monsonite/TICK_TALK/TICK_04_08_24.jpg

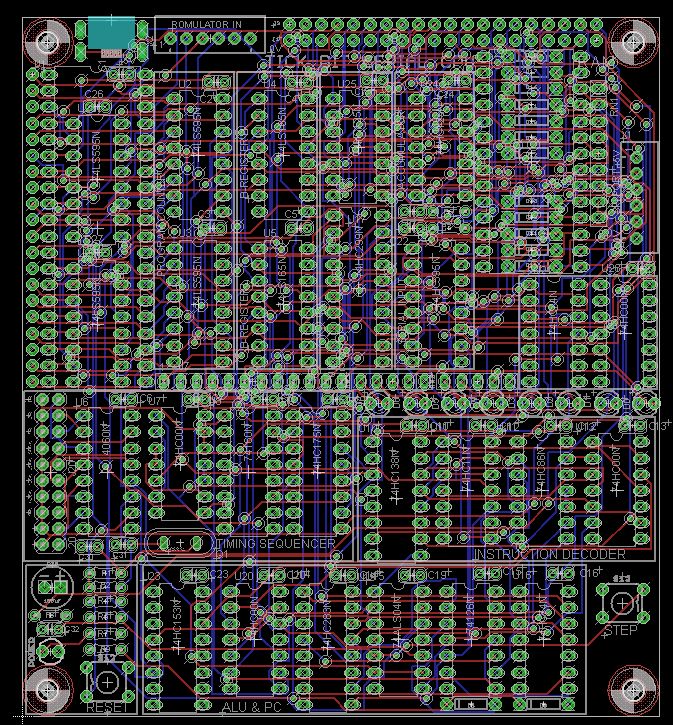
TICK_04_08_24.jpg
