monsonite/TICK_TALK/ALU_PC_schematic.jpg

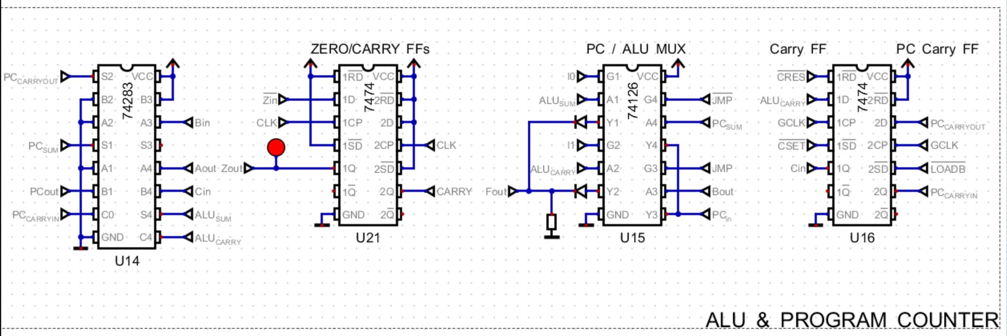
ALU_PC_schematic.jpg
