monsonite/TICK_TALK/Prototype_Program_Counter.jpg

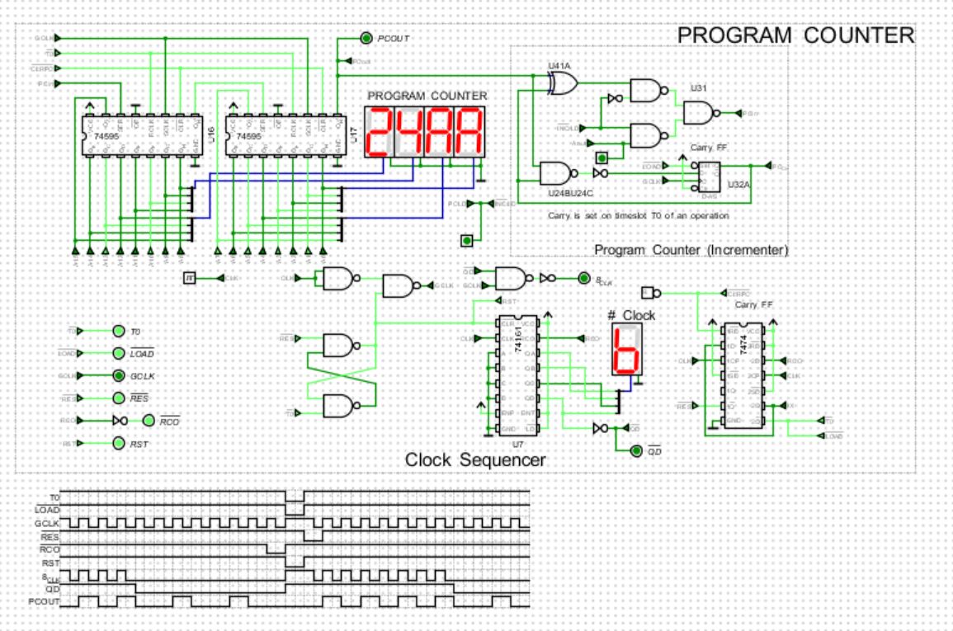
Prototype_Program_Counter.jpg
