monsonite/TICK_TALK/TPG_schematic.jpg

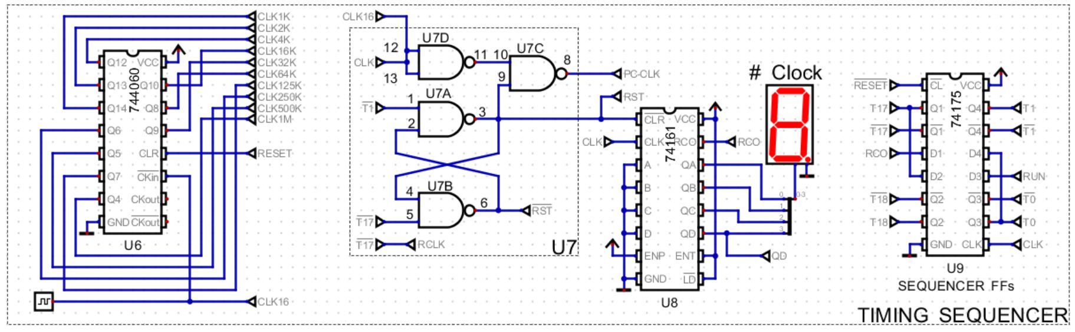
TPG_schematic.jpg
