monsonite/TICK_TALK/Build_step_1A_TPG.jpg

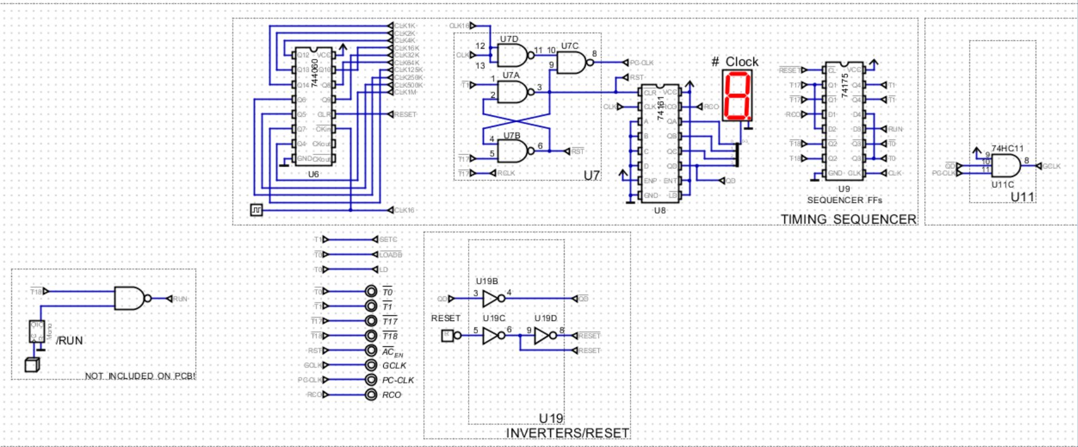
Build_step_1A_TPG.jpg
