monsonite/TICK_TALK/Build_Step_3A_ROMulator.jpg

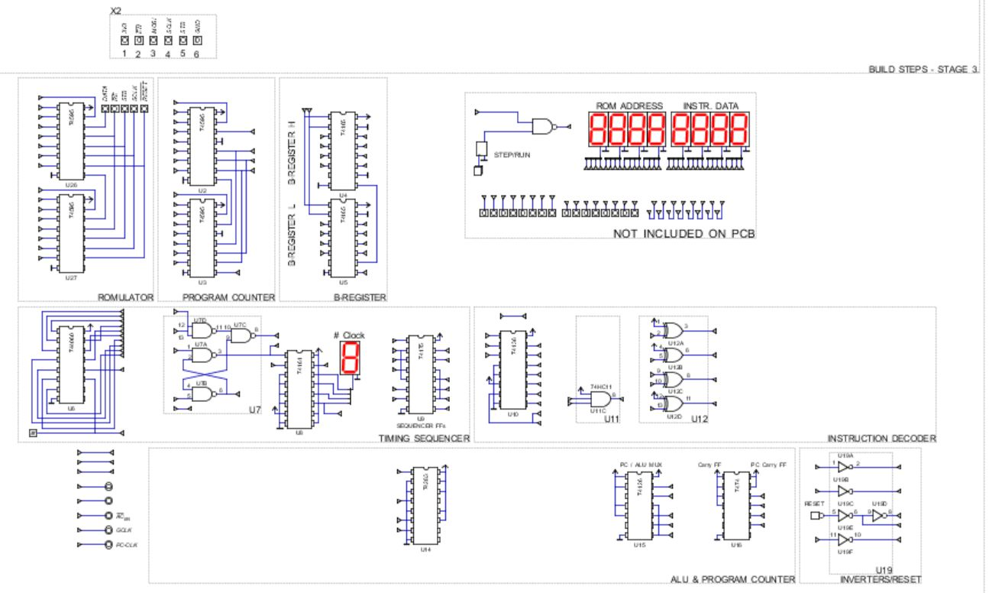
Build_Step_3A_ROMulator.jpg
