monsonite/TICK_TALK/Build_step_4A_ALU_Instruction_Decoder.jpg

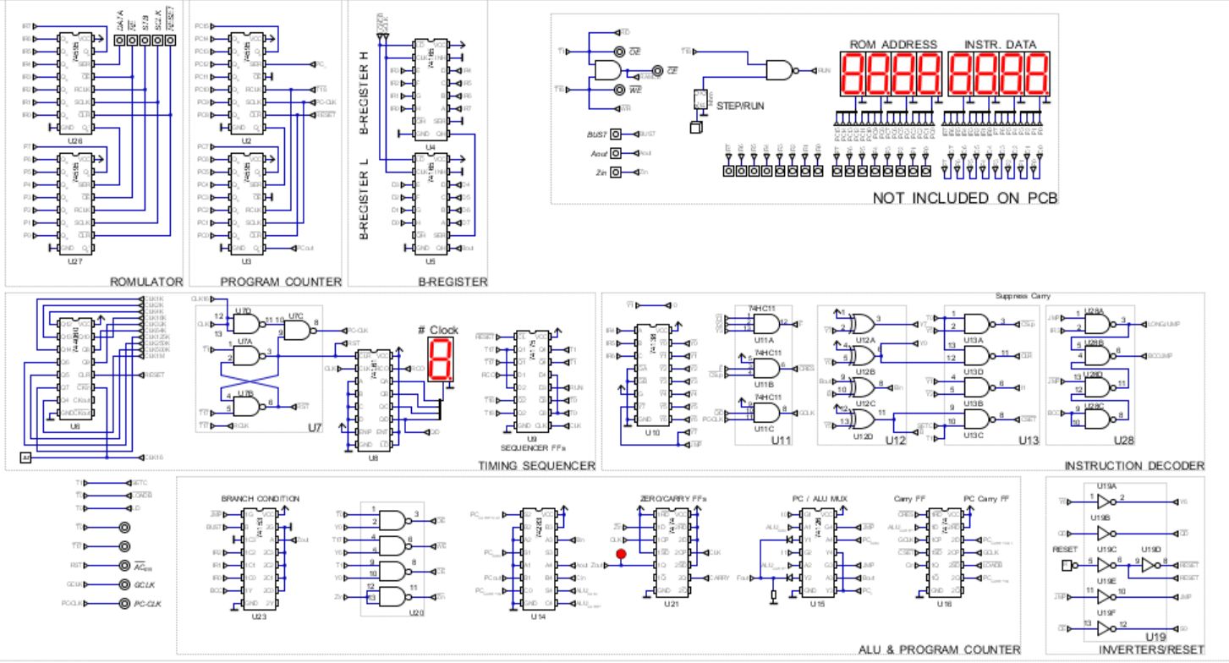
Build_step_4A_ALU_Instruction_Decoder.jpg
