monsonite/TICK_TALK/Build_Step_5A_RAM_Buffers_Accumulator_Serial_Input.jpg

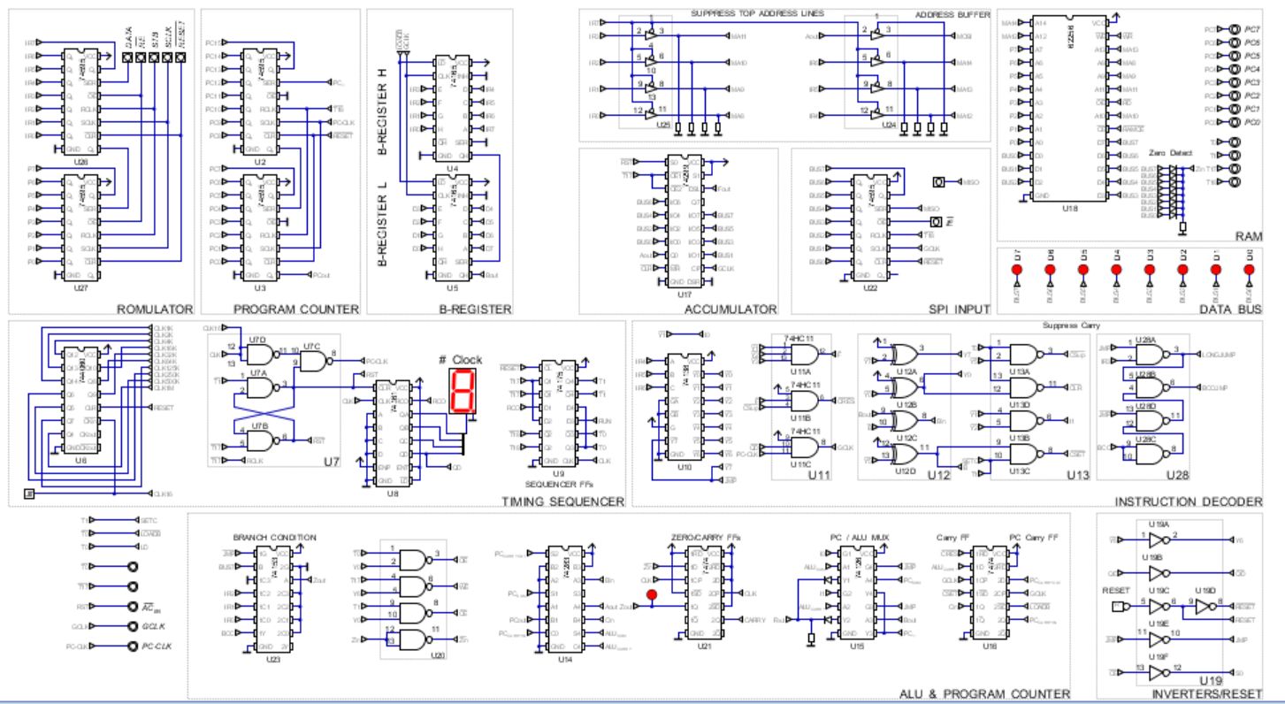
Build_Step_5A_RAM_Buffers_Accumulator_Serial_Input.jpg
