monsonite/TICK_TALK/Bulid_step_2A_B-reg_PC.jpg

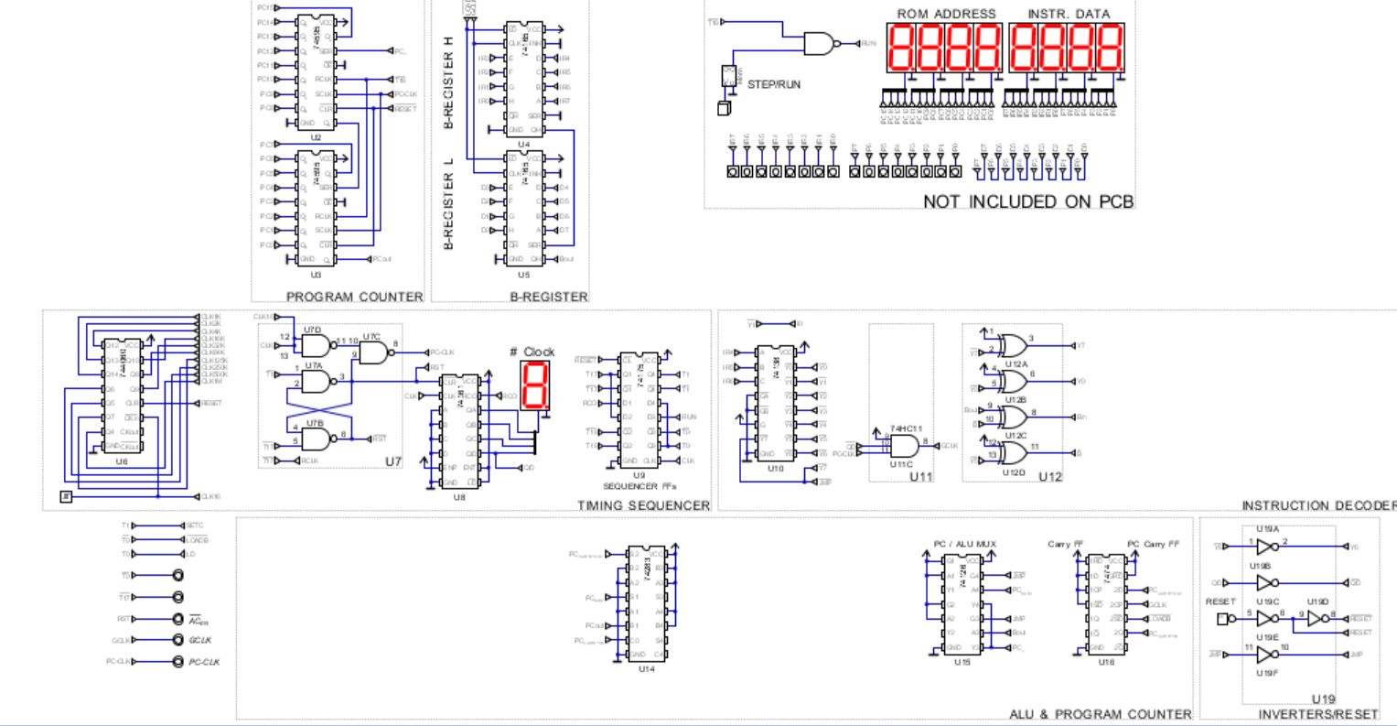
Bulid_step_2A_B-reg_PC.jpg
