monsonite/TICK_TALK/Instruction_Decoder_schematic.jpg

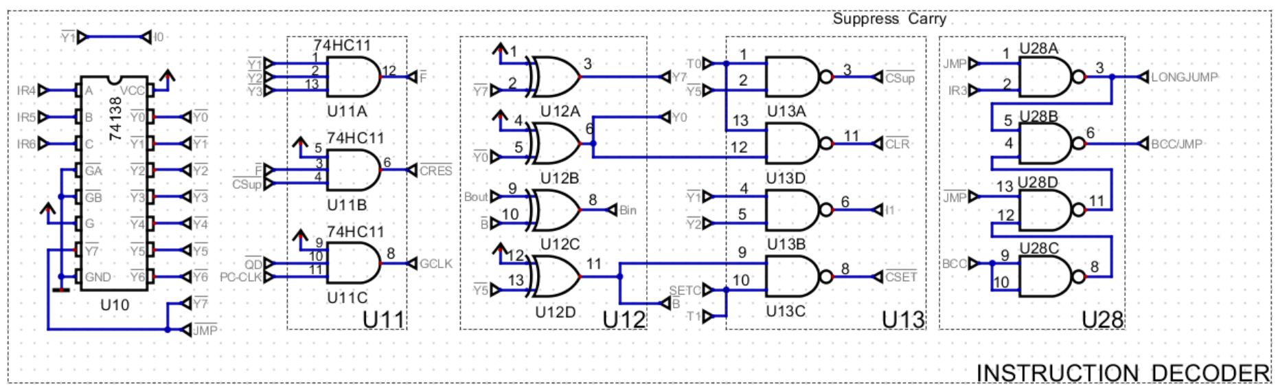
Instruction_Decoder_schematic.jpg
